tkilla64/bb2-sequencer/sw/bassbuddy2/presets.h

/** 
* @file preset.h
* 
* const data used for pattern presets
*
*/

#ifndef _inc_preset
#define _inc_preset

#include <stdio.h>
#include "sequencer.h"

// <--- insert preset code here --->
const seq_step_t pres_ptn[PRESETS][MAXSTEPS] = {
  {
    0x00, 0x00, 0x00, 0x00,
    0x0d, 0x00, 0x01, 0x00,
    0x0d, 0x00, 0x0a, 0x00,
    0x0d, 0x00, 0x05, 0x00,
    0x00, 0x00, 0x00, 0x00,
    0x0d, 0x00, 0x01, 0x00,
    0x0d, 0x00, 0x08, 0x00,
    0x0d, 0x00, 0x05, 0x00,
    0x00, 0x00, 0x00, 0x00,
    0x0d, 0x00, 0x01, 0x00,
    0x0d, 0x00, 0x0a, 0x00,
    0x0d, 0x00, 0x05, 0x00,
    0x00, 0x00, 0x00, 0x00,
    0x0d, 0x00, 0x01, 0x00,
    0x0d, 0x00, 0x08, 0x00,
    0x0d, 0x00, 0x05, 0x00,
  },

  {
    0x01, 0x00, 0x00, 0x00,
    0x00, 0x00, 0x00, 0x00,
    0x0d, 0x00, 0x05, 0x00,
    0x00, 0x00, 0x00, 0x00,
    0x00, 0x00, 0x00, 0x00,
    0x0d, 0x00, 0x00, 0x00,
    0x00, 0x00, 0x00, 0x00,
    0x00, 0x00, 0x00, 0x00,
    0x00, 0x00, 0x00, 0x00,
    0x00, 0x00, 0x00, 0x00,
    0x0d, 0x00, 0x05, 0x00,
    0x0d, 0x00, 0x0f, 0x00,
    0x00, 0x00, 0x00, 0x00,
    0x0d, 0x00, 0x00, 0x00,
    0x00, 0x00, 0x00, 0x00,
    0x00, 0x00, 0x00, 0x00,
  },

  {
    0x0d, 0x00, 0x00, 0x00,
    0x0d, 0x00, 0x00, 0x00,
    0x00, 0x00, 0x00, 0x00,
    0x0d, 0x00, 0x00, 0x00,
    0x0d, 0x00, 0x00, 0x00,
    0x0d, 0x00, 0x00, 0x00,
    0x00, 0x00, 0x00, 0x00,
    0x0d, 0x00, 0x00, 0x00,
    0x0d, 0x00, 0x00, 0x00,
    0x0d, 0x00, 0x00, 0x00,
    0x00, 0x00, 0x00, 0x00,
    0x0d, 0x00, 0x00, 0x00,
    0x0d, 0x00, 0x00, 0x00,
    0x0d, 0x00, 0x00, 0x00,
    0x00, 0x00, 0x00, 0x00,
    0x0d, 0x00, 0x00, 0x00,
  },

  {
    0x01, 0x00, 0x00, 0x00,
    0x0d, 0x00, 0x00, 0x00,
    0x0d, 0x00, 0x00, 0x00,
    0x19, 0x00, 0x00, 0x00,
    0x14, 0x00, 0x00, 0x00,
    0x08, 0x00, 0x00, 0x00,
    0x0d, 0x00, 0x0a, 0x00,
    0x19, 0x00, 0x00, 0x00,
    0x0d, 0x00, 0x00, 0x00,
    0x20, 0x00, 0x00, 0x00,
    0x0d, 0x00, 0x00, 0x00,
    0x14, 0x00, 0x00, 0x00,
    0x11, 0x00, 0x00, 0x00,
    0x0d, 0x00, 0x00, 0x00,
    0x14, 0x00, 0x02, 0x00,
    0x0d, 0x00, 0x00, 0x00,
  },

  {
    0x0d, 0x00, 0x00, 0x00,
    0x0d, 0x00, 0x00, 0x00,
    0x0d, 0x00, 0x00, 0x00,
    0x0d, 0x00, 0x00, 0x00,
    0x0d, 0x00, 0x00, 0x00,
    0x0d, 0x00, 0x00, 0x00,
    0x0f, 0x00, 0x00, 0x00,
    0x0d, 0x00, 0x00, 0x00,
    0x0d, 0x00, 0x00, 0x00,
    0x0d, 0x00, 0x00, 0x00,
    0x0d, 0x00, 0x0f, 0x00,
    0x0d, 0x00, 0x00, 0x00,
    0x0f, 0x00, 0x06, 0x00,
    0x20, 0x00, 0x10, 0x00,
    0x08, 0x00, 0x00, 0x00,
    0x0f, 0x00, 0x00, 0x00,
  },

};


const uint16_t pres_prop[PRESETS] = {
    0x001f,     0x002f,     0x005f,     0x007f,     0x009f,
};
// <------------------------------->
#endif
